MeckPetarda/bachelor/write/outline/3.3_firmware.md

# OSNOVA PLUS - 3.3 firmware

---

- Firmware is written in C using ESP-IDF v5.x with FreeRTOS; the entire application runs on a single ESP32-WROOM-32
  module
- The dual-core Xtensa LX6 architecture allows separation of concerns: the WiFi stack is pinned to Core 0 by ESP-IDF
  configuration, leaving Core 1 available for application logic including RFID communication and the main task loop (per
  ESP32 TRM Section 1.1)
- The firmware is identical across all Lighthouse units - no unit-specific configuration is compiled in; all per-device
  settings (WiFi credentials, MQTT broker address, lighthouse identity) are configured at runtime via the provisioning
  system and stored in NVS

## 3.3.1 system initialization and WiFi provisioning

- On boot, the firmware executes a sequential initialization: GPIO configuration -> battery monitor -> WiFi provisioning
  (credentials load + STA connection) -> SNTP time synchronisation (broker IP as NTP server) -> MQTT client -> offline
  event logger -> RFID reader -> main task loop
- If the device has never been configured (no credentials in NVS), the boot sequence blocks after GPIO initialization
  and waits for the user to trigger provisioning via a 5-second hold of BUTTON2

### Provisioning flow

- Provisioning is triggered by a 5-second hold of BUTTON2, which sets a flag in RTC memory and calls `esp_restart()`; on
  the subsequent boot, the firmware detects the flag and enters AP mode instead of STA mode
- In AP mode, the device broadcasts an open WiFi network ("Lighthouse-Setup") and starts an HTTP server on port 80
  serving a minimal HTML configuration form from firmware flash via the SPIFFS virtual filesystem
- A lightweight DNS server responds to all DNS queries with the device's AP IP address (192.168.4.1), enabling captive
  portal detection on iOS, Android, Windows, and macOS; the user's device automatically opens a browser to the
  provisioning page
- The form collects four fields: WiFi SSID, WiFi password, MQTT broker IP, and MQTT broker port; client-side JavaScript
  validates input format before submission
- On form submission, the device attempts a STA connection with the provided WiFi credentials; if successful, it tests
  MQTT connectivity; results are reported back to the browser via a JSON response
- The browser displays success/failure and a restart button; the device only restarts when the user explicitly clicks
  restart, ensuring the browser receives the response before the AP shuts down
- Credentials are encrypted with AES-128-ECB via the mbedTLS library, which utilises the ESP32 hardware AES accelerator
  (per ESP32 TRM Section 14), and stored in a dedicated NVS partition; on subsequent boots, credentials are loaded from
  NVS and used for automatic STA connection

Figure 3.3.1-1: Provisioning state machine diagram - states: UNCONFIGURED, SETUP_REQUESTED, AP_ACTIVE, CONNECTING, CONNECTED, OFFLINE; transitions labelled with triggering events (button press, credential submission, connection success/failure, reboot)

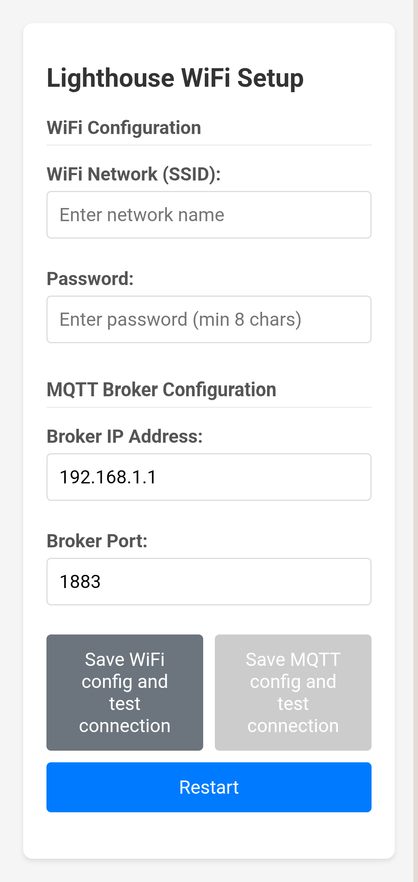
[picture p8: write/outline/images/3.3.1-2_page.png]
Figure 3.3.1-2: Screenshot of the provisioning web form as rendered on a mobile device - showing WiFi SSID/password fields, MQTT broker IP/port fields, test buttons, and status display area


## 3.3.2 UHF RFID scan control

- The YPD-R300 UHF RFID reader module communicates with the ESP32 via UART at 115 200 baud (per R300 Protocol Section
  1.2)
- RFID scanning uses the real-time inventory command `cmd 0x89` (`cmd_name_real_time_inventory`) with channel parameter
  `0xFF` (minimized inventory duration) and 10 ms inter-round delay (per R300 Protocol Section 2.2.8)
- In real-time inventory mode, the reader streams tag detection packets as they occur rather than buffering them
  internally; each packet contains the tag's EPC, RSSI, frequency/antenna ID, and protocol control (PC) word
- A scan window lasts approximately 5 seconds, producing ~60 individual tag detections per window under typical
  conditions

### IR-triggered scanning

- The AM312 PIR sensor on GPIO19 detects motion in the doorway and triggers RFID scan bursts via a GPIO interrupt
  (rising edge, `IRAM_ATTR` ISR handler)
- On IR trigger, the firmware powers on the R300 module via the BC337-25 transistor switch, performs a UART handshake to
  verify reader responsiveness, and starts real-time inventory
- The scan burst runs for `IR_SCAN_DURATION_MS` (default 5 s); if additional IR triggers arrive during an active
  burst, the timer is restarted without interrupting the ongoing inventory - this extends the scan window when a person
  lingers in the doorway
- When the burst timer expires with no further IR triggers, the inventory is stopped and the R300 module is powered off
  to conserve energy

### MQTT batch accumulator

- To avoid saturating the MQTT connection with ~60 individual publishes during a 5-second scan window, detections are
  accumulated in a time-windowed batch buffer on the firmware side
- The accumulator collects tag detections for up to `scan_batch_ms` (default 150 ms, configurable 50-2 000 ms) or until
  the buffer reaches `MQTT_SCAN_BATCH_MAX_ENTRIES`, then flushes the batch as a single JSON array to MQTT topic
  `lighthouse/{id}/scans`
- Each element in the flushed array carries its individual `epc`, `rssiDbm`, `antennaId`, `frequency`, and `deviceId`
  fields; the `timestampMs` and `timeBasis` fields are computed once at flush time and are shared across all elements in
  the batch - timestamp resolution is therefore bounded by the batch interval (minimum 50 ms, default 150 ms)
- The live scan publish path uses QoS 1 to reduce the four-way handshake overhead of QoS 2; the offline replay path
  retains QoS 2 for exactly-once delivery of historically cached events

### Power cap discovery

- The YPD-R300 hardware power cap is 25 dBm, despite the datasheet specifying 33 dBm; the `set_power(33)` command
  returns error code `0x48` (parameter out of range) which was initially ignored due to missing response validation
- The firmware now reads and validates all R300 command responses; transmit power is clamped to the 20-25 dBm range

## 3.3.3 timekeeping and timestamp quality

- The ESP32 does not include a battery-backed hardware RTC; after a power cycle, the system clock starts from an
  undefined epoch and must be synchronised via SNTP before timestamps are meaningful
- The firmware implements a three-tier time quality model to ensure that every event payload declares the
  trustworthiness of its timestamp

**Table 3.3.3-1** - Time quality tiers

| Quality level | `timeBasis` value | Condition | Accuracy |
| --- | --- | --- | --- |
| Synced | `synced` | SNTP synchronisation completed successfully | Millisecond-level (network + NTP jitter) |
| Estimated | `estimated` | No SNTP sync yet, but last-known-good time recovered from NVS | Seconds to minutes (RTC drift ~5 % at 150 kHz; per ESP32 Datasheet Section 3.3.4) |
| Relative | `relative` | No NVS time available; first boot or NVS lost | Boot-relative milliseconds only; not a real wall-clock time |

### SNTP synchronisation

- The firmware uses the ESP-IDF SNTP client in polling mode against a chrony NTP server on the local network
- On successful sync, a callback upgrades the time quality to `synced` and persists the current Unix timestamp alongside
  the ESP32 uptime counter to NVS; this pair allows the next boot to estimate wall-clock time even before SNTP completes
- Timezone is set to CET/CEST (`TZ=CET-1CEST,M3.5.0,M10.5.0/3`) before SNTP initialisation so that `localtime()` returns
  correct local time immediately on sync

### Offline degradation

- If SNTP sync does not complete (e.g. NTP server unreachable), the firmware continues operating with `estimated` or
  `relative` timestamps
- The `timeBasis` field is attached to every scan event payload; the server uses this to decide whether scans are
  eligible for direction detection processing - non-synced scans are handled by the orphan processing logic on the
  server side

## 3.3.4 MQTT communication and offline caching

### MQTT client

- The firmware connects to the MQTT broker using the `esp_mqtt_client` component with connection parameters loaded from
  NVS (broker IP and port configured during provisioning)
- The MQTT client ID is derived from the ESP32's eFuse MAC address, ensuring uniqueness across devices (per ESP32 TRM
  Section 4.4)
- A Last Will and Testament (LWT) message is registered on connect, allowing the server to detect unexpected
  disconnections

**Table 3.3.4-1** - MQTT topics and QoS levels

| Topic | Direction | QoS | Content |
| --- | --- | --- | --- |
| `lighthouse/{id}/scans`  | Publish (live) | 1 | Batched JSON array of tag detections |
| `lighthouse/{id}/scans`  | Publish (replay) | 2 | Replayed offline-cached events |
| `lighthouse/{id}/health` | Publish | 1 | Periodic health telemetry (system, RFID, battery) |
| `lighthouse/{id}/config` | Subscribe | 1 | Runtime configuration updates from server |

### Offline event caching

- When the MQTT connection is unavailable, tag detections are stored to a dedicated LittleFS partition on the ESP32's
  flash memory; this is a separate partition from the SPIFFS partition used by the provisioning HTML - SPIFFS is a
  read-only image compiled into the firmware binary, while LittleFS is a writable filesystem used exclusively for
  offline event storage
- Events are written to a ring buffer file (`events.bin`) with CRC32 validation per entry; write and read indices are
  persisted to both RTC memory (survives soft reset) and NVS (survives power loss)
- On MQTT reconnection, a background replay task reads cached events and publishes them at a throttled rate (max 10
  events/second) with QoS 2, adding an `offline: true` flag and a `replayTime` field to each payload
- The replay task runs at lower priority than the main logging task, ensuring real-time detections are not delayed by
  replay activity

Figure 3.3.4-1: Offline caching and replay sequence diagram - tag detected while offline -> event queued -> logging task writes to LittleFS ring buffer -> NVS pointers updated -> MQTT reconnects -> replay task reads from ring buffer -> publishes with offline flag -> server ingests as normal scan wi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

## 3.3.5 user interaction: buttons, LEDs, and gestures

- The IO subsystem manages four LEDs, two buttons, and one IR sensor; all IO logic is encapsulated in a dedicated
  `io_controller` module, keeping the main application file (`lighthouse.c`) limited to orchestration and MQTT/offline
  routing

**Table 3.3.5-1** - GPIO pin assignments

| Constant | GPIO | Function |
| --- | ---- | --- |
| LED1_PIN | 4 | WiFi + MQTT combined status (green) |
| LED2_PIN | 21 | IR mode / AP provisioning indicator (green) |
| SCANNING_LED  | 26 | Active RFID scan indicator (red) |
| ACTIVITY_LED  | 25 | Tag detection flash / battery status (yellow) |
| BUTTON1_PIN | 22 | Scan mode control |
| BUTTON2_PIN | 23 | Status message / WiFi setup trigger |
| IR_SENSOR_PIN | 19 | AM312 PIR motion sensor |

- GPIO22 and GPIO23 (buttons) use external pull-up resistors; debounce filtering is applied in software with a 50 ms
  debounce threshold

### Scan modes

- The firmware operates in one of two scan modes, selectable via BUTTON1 3-second hold:

**Table 3.3.5-2** - Scan mode behavior

| Mode | LED2 state | IR sensor | BUTTON1 short press | Entry condition |
| --- | --- | --- | --- | --- |
| IR Mode (default) | Solid on | Active - triggers 5 s scan bursts | No-op | 3 s hold from Manual / Boot |
| Manual Mode | Off | Ignored | Toggle RFID on/off  | 3 s hold from IR Mode |

- RFID scanning is always stopped and the reader powered off before any mode transition

Figure 3.3.5-1: Scan mode state machine - two states (IR Mode, Manual Mode); transitions: 3-second BUTTON1 hold in either direction; entry actions listed for each state (stop RFID, set LED2, enable/disable IR)

### Button gestures

**Table 3.3.5-3** - Complete button gesture reference

| Button  | Gesture | Action |
| --- | --- | --- |
| BUTTON1 | Short press | Toggle RFID scan (Manual Mode only; no-op in IR Mode) |
| BUTTON1 | 3 s hold | Switch between IR Mode and Manual Mode |
| BUTTON2 | Short press | Publish status/statistics message via MQTT |
| BUTTON2 | 5 s hold | Enter WiFi AP provisioning (triggers reboot into setup mode) |
| Both | 10 s hold | Cache purge: clear offline event cache, confirmation LED sequence, restart |

### Cache purge combo gesture

- Holding both buttons simultaneously for 10 seconds triggers a developer cache purge gesture
- During the hold, LEDs illuminate sequentially as a countdown: LED1 at 2.5 s, LED2 at 5 s, ACTIVITY_LED at 7.5 s
- At 10 s, `offline_logger_clear_all()` resets the ring buffer pointers; a confirmation flash sequence (each LED flashed
  in order, 200 ms on/off) plays before `esp_restart()`
- Releasing either button before the 10-second threshold cancels the gesture and restores normal LED states
- While the combo gesture is active, RFID scanning is stopped and IR triggers are suppressed

### LED indicator behavior

**Table 3.3.5-4** - LED states during normal operation

| LED | Condition | State |
| --- | --- | --- |
| LED1 (green) | No WiFi connection | Off |
| LED1 (green) | WiFi connected, no MQTT | Blinking 1 s period |
| LED1 (green) | WiFi + MQTT connected | Solid on |
| LED2 (green) | IR Mode active | Solid on |
| LED2 (green) | Manual Mode active | Off |
| SCANNING_LED (red) | RFID inventory in progress | On |
| SCANNING_LED (red) | No active inventory | Off |
| ACTIVITY_LED (yellow) | Tag detected | Brief 100 ms flash  |

**Table 3.3.5-5** - LED states during AP provisioning

| LED | Provisioning phase | State |
| --- | --- | --- |
| LED1 (green) | AP active, WiFi test not yet passed | Blinking |
| LED1 (green) | WiFi test passed | Solid on |
| LED2 (green) | AP active, MQTT test not yet passed | Blinking |
| LED2 (green) | MQTT test passed | Solid on |

### Battery status LED patterns (ACTIVITY_LED, battery power only)

| Battery level  | LED pattern |
| --- | --- |
| USB powered | Off (tag detection flashes only) |
| Battery > 10 % | Brief flash every 5 seconds |
| Battery 5-10 % | Pulsing 500 ms on/off |
| Battery < 5 %  | Rapid pulsing 200 ms on/off |

- The battery LED patterns run in a dedicated FreeRTOS task and do not interfere with the brief 100 ms tag detection
  flashes on the same LED
