MeckPetarda/bachelor/presentation/beta/Beta.odp

## EMBEDDED ŘEŠENÍ DOCHÁZKOVÉHO SYSTÉMU PRO INTEGRACI DO PODNIKOVÉ APLIKACE

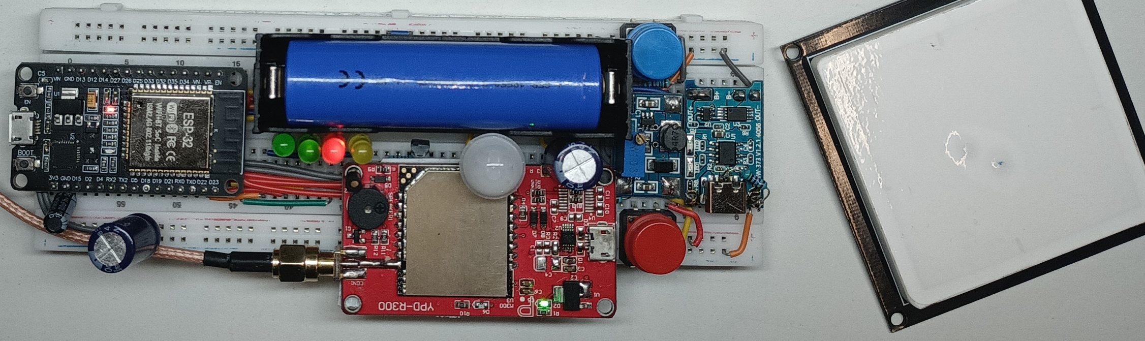
[picture p11: figure]

Ústav mechaniky těles, mechatroniky a biomechaniky
Fakulta strojního inženýrství, Vysoké učení technické v Brně

2026

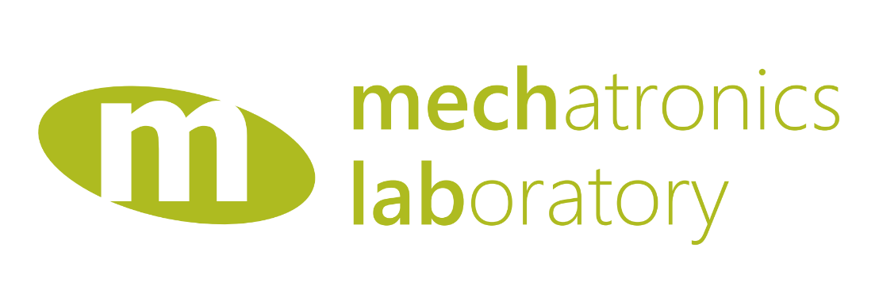
[picture p12: figure]

Autor práce: Jakub Hloušek

Vedoucí práce: Ing. Michal Bastl, Ph.D

Autor práce: Jakub Hloušek

Vedoucí práce: Ing. Michal Bastl, Ph.D

Notes: <number>

## Zadání a cíle

1. Rešerše aktuálních řešení a technologií
2. Návrh architektury docházkového systému
3. Implementace prototypu zahrnujícího identifikační modul (RFID/NFC/PIN)
4. Ověření funkčnosti řešení v modelové kancelářské situaci

0<number> / 11

## Motivace – stávající systémy

Čipové (RFID, PIN)

- jedno čidlo
- krátká vzdálenost pro sken

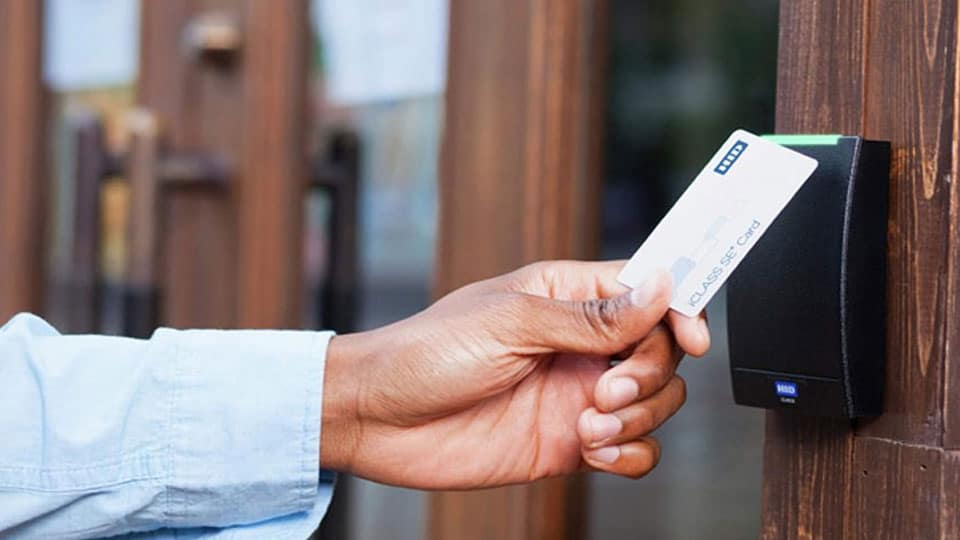
[picture p13: figure]

Biometrické

- vysoká cena
- práce s citlivými informacemi

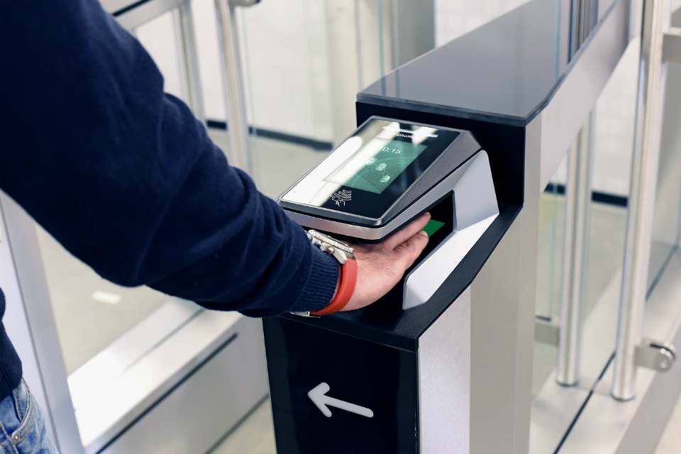
[picture p14: figure]

0<number> / 11

## Motivace – navrhnuté řeření

- Dvě čipové brány s technologií UHF RFID
- Pasivní sken čipu na 2-3m (dle antény)
- Levné provedení
- Nepracuje s citlivými informacemi

0<number> / 11

## Motivace – navrhnuté řeření


- Dvě čipové brány s technologií UHF RFID
- Pasivní sken čipu na 2-3m (dle antény)
- Levné provedení
- Nepracuje s citlivými informacemi

0<number> / 11

## Co je hotovo

- 2x Prototyp UHF RFID majáků na breadboardech
- Navržena DPS - připravena k osazení
- Funkční firmware pro ESP-32
- Přenos informací na server
- Koncept webového klienta s debugem skenů

0<number> / 11

## Slide 7

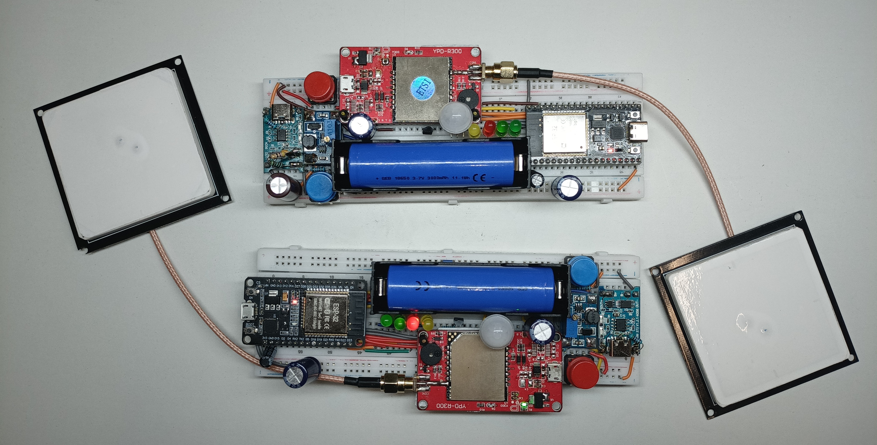
[picture p15: figure]

0<number> / 11

## Slide 8

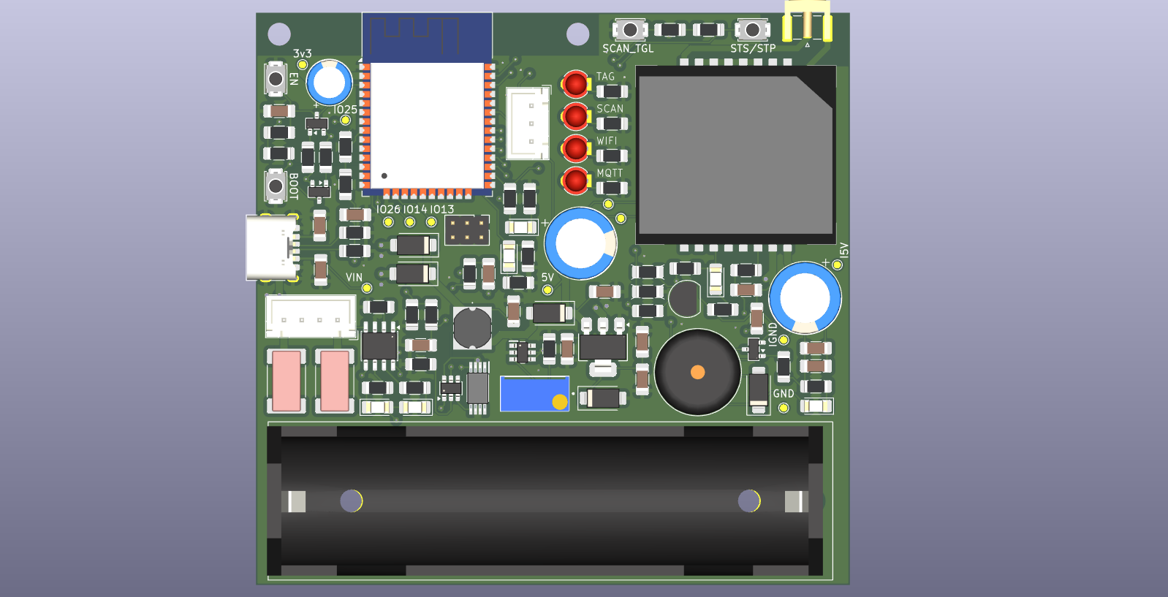
[picture p16: figure]

0<number> / 11

## Co je v plánu

- Osazení desky
- Vytvoření pouzdra pro maják
- Správa uživatelů a majáků na webu
- Zpracování surových dat na časové bloky
- Integrace s externím softwarem

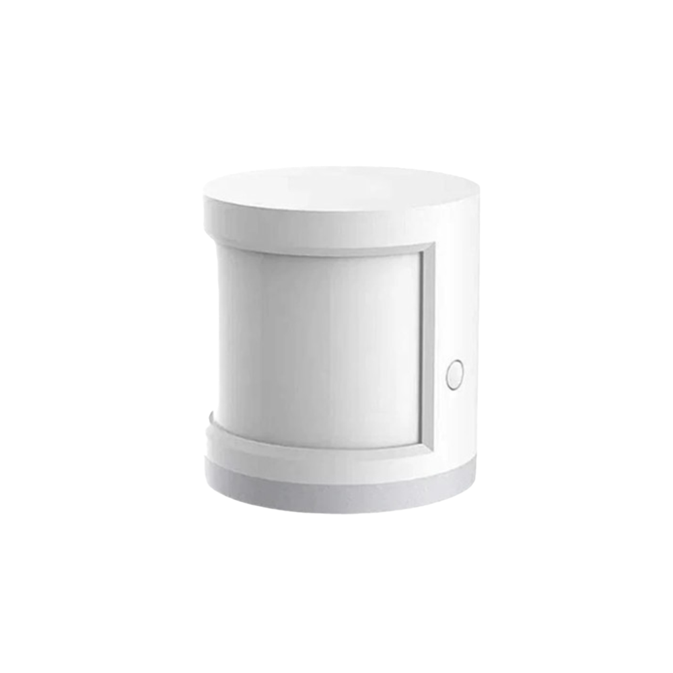
[picture p17: figure]

0<number> / 11

## Současný stav

Hardware

Software

Praktický test

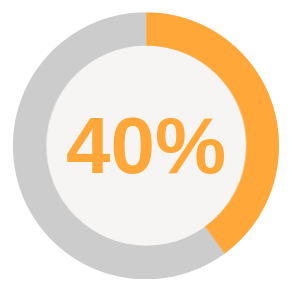
[picture p18: figure]
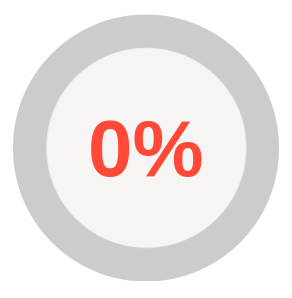
[picture p19: figure]

Firmware

Návrh pouzdra

Napsat práci

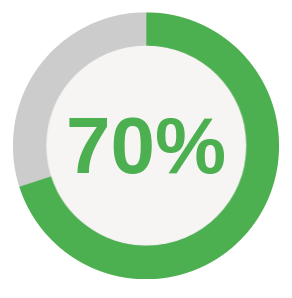
[picture p20: figure]
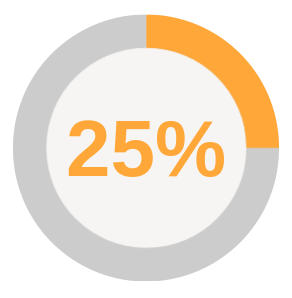
[picture p21: figure]

<number> / 11

## Děkuji za pozornost

Ústav mechaniky těles, mechatroniky a biomechaniky
Fakulta strojního inženýrství, Vysoké učení technické v Brně

2026

Autor práce: Jakub Hloušek

Vedoucí práce: Ing. Michal Bastl, Ph.D

Notes: <number>
