MeckPetarda/bachelor/docs/pinout.webp

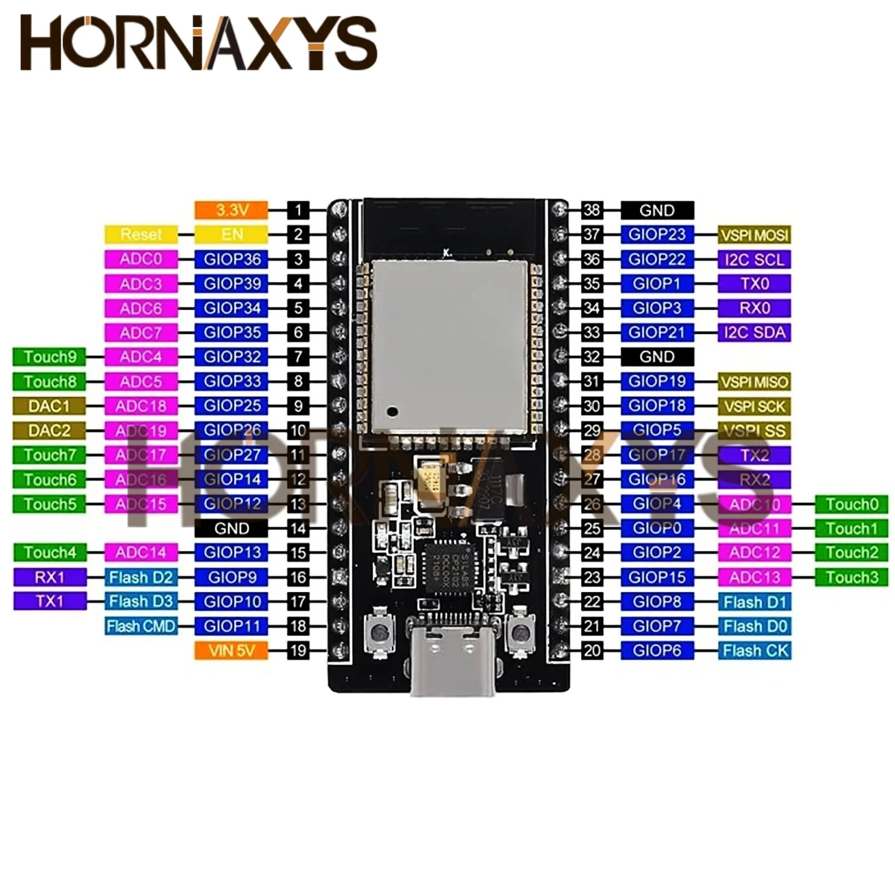
docs/pinout.webp
