MeckPetarda/bachelor/write/thesis/images/board_v2_schematic.png

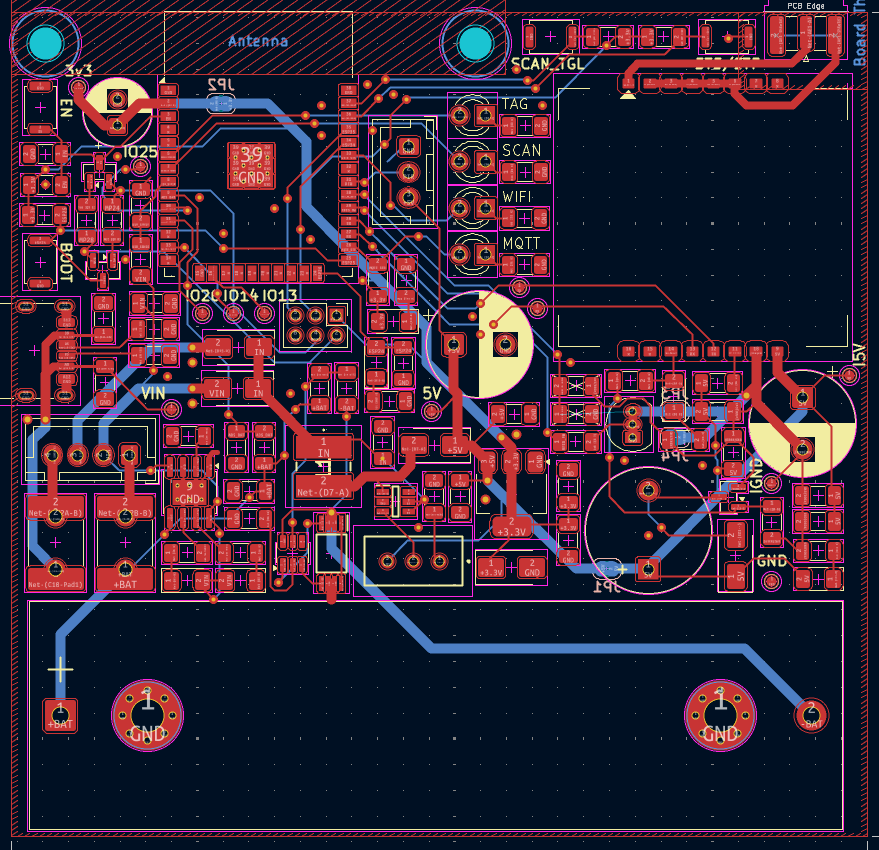
write/thesis/images/board_v2_schematic.png
