MeckPetarda/bachelor/write/thesis/images/kicad_render.png

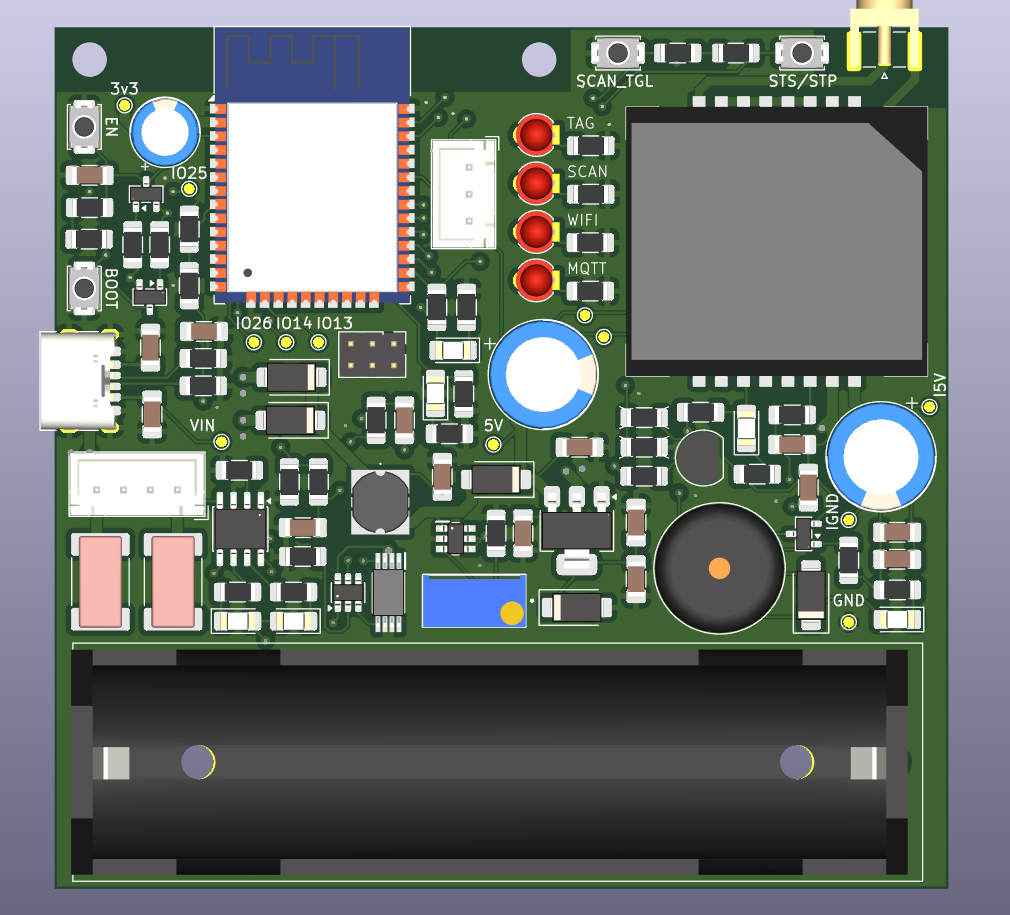
write/thesis/images/kicad_render.png
