MeckPetarda/bachelor/write/thesis/images/lighthouses.jpg

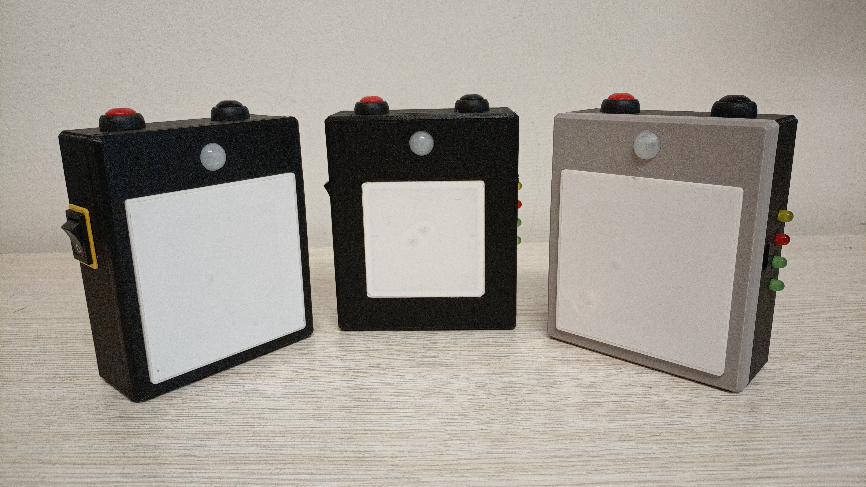
write/thesis/images/lighthouses.jpg
