MeckPetarda/bachelor/write/thesis/images/kicad_render_vs_assembly.png

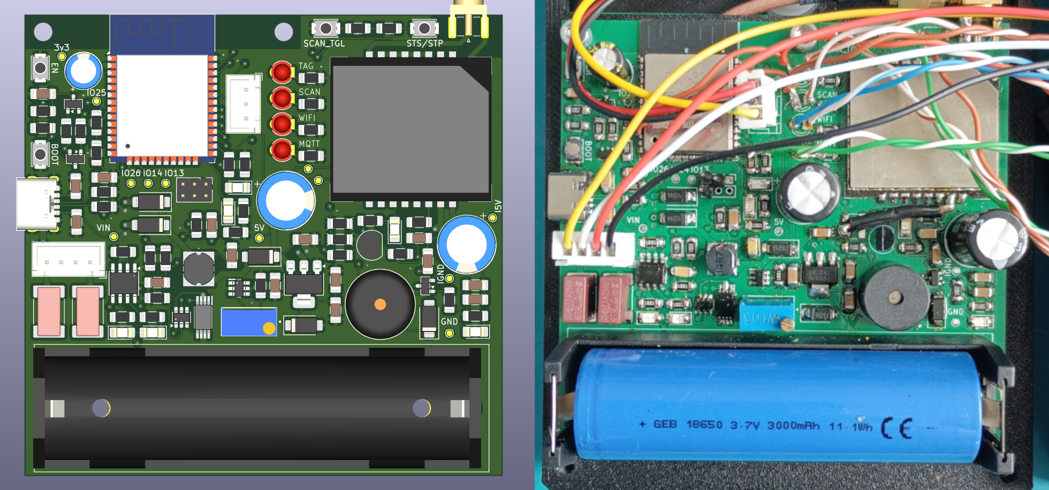
write/thesis/images/kicad_render_vs_assembly.png
