MeckPetarda/bachelor/circuits/lighthouse/lighthouse_v2.pdf

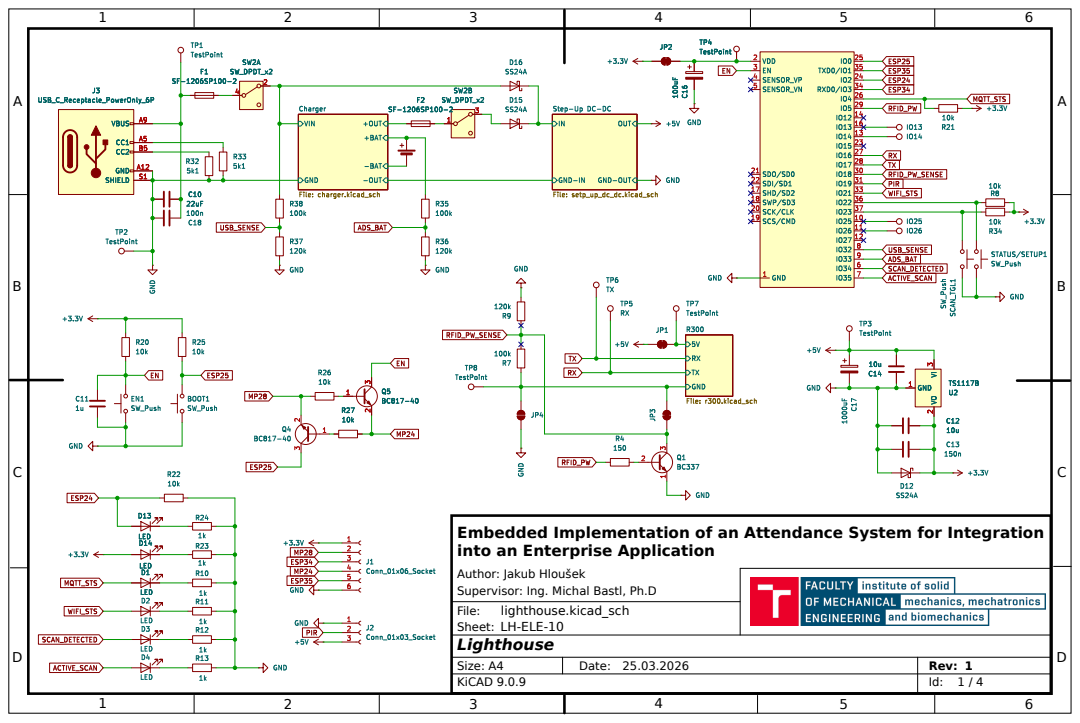
[picture p52: page 1]
Size: A4; Date: 25.03.2026; Rev: 1; LH-ELE-10; lighthouse.kicad_sch

Embedded Implementation of an Attendance System for Integration
into an Enterprise Application
Author: Jakub Hloušek
Supervisor: Ing. Michal Bastl, Ph.D
File:
Sheet:
Lighthouse
KiCAD 9.0.9

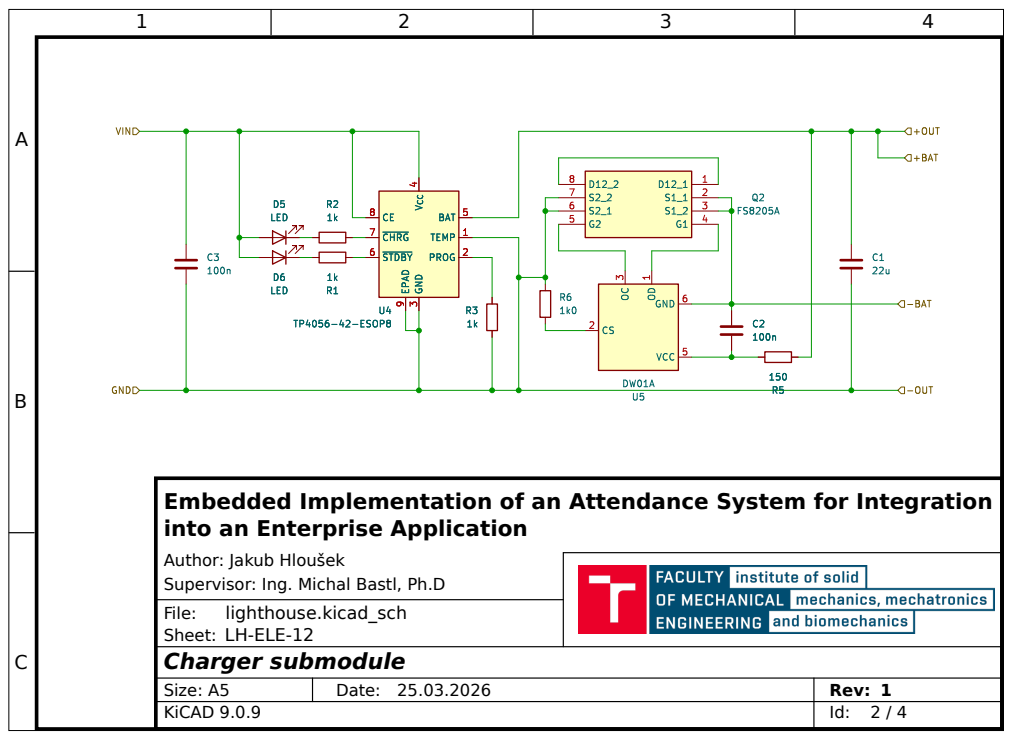
[picture p53: page 2]
Size: A5; Date: 25.03.2026; Rev: 1; LH-ELE-12; lighthouse.kicad_sch

Embedded Implementation of an Attendance System for Integration
into an Enterprise Application
Author: Jakub Hloušek
Supervisor: Ing. Michal Bastl, Ph.D
File:
Sheet:
Charger submodule

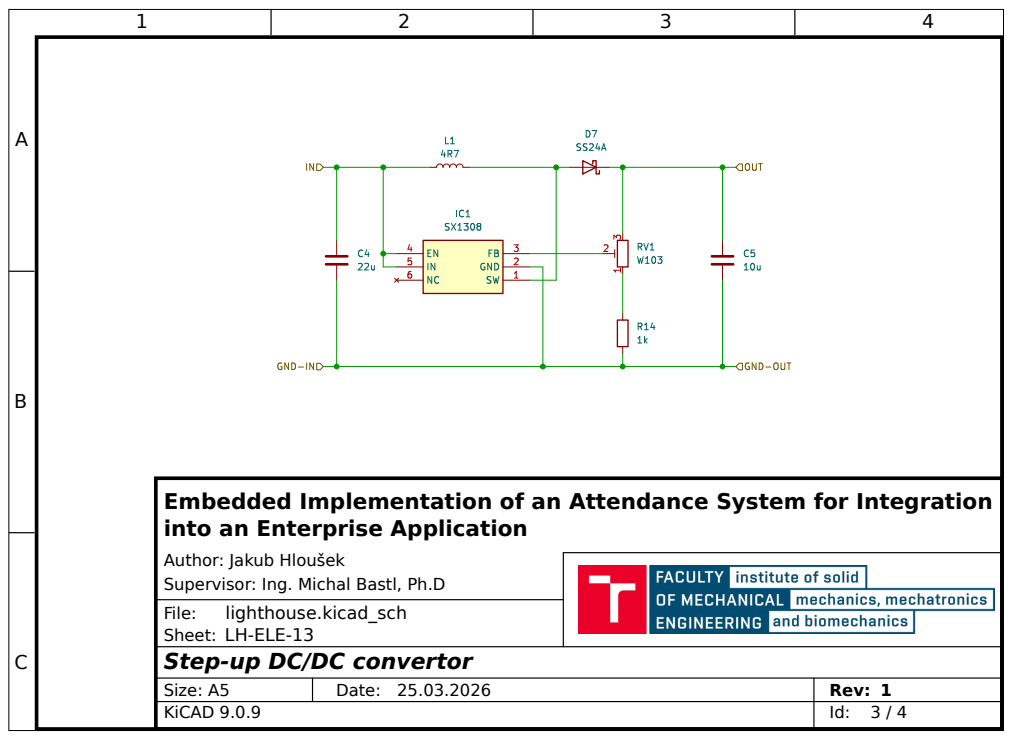
[picture p54: page 3]
ion; Size: A5; Date: 25.03.2026; Rev: 1; LH-ELE-13; lighthouse.kicad_sch

Embedded Implementation of an Attendance System for Integration
into an Enterprise Application
Author: Jakub Hloušek
Supervisor: Ing. Michal Bastl, Ph.D
File:
Sheet:
Step-up DC/DC convertor

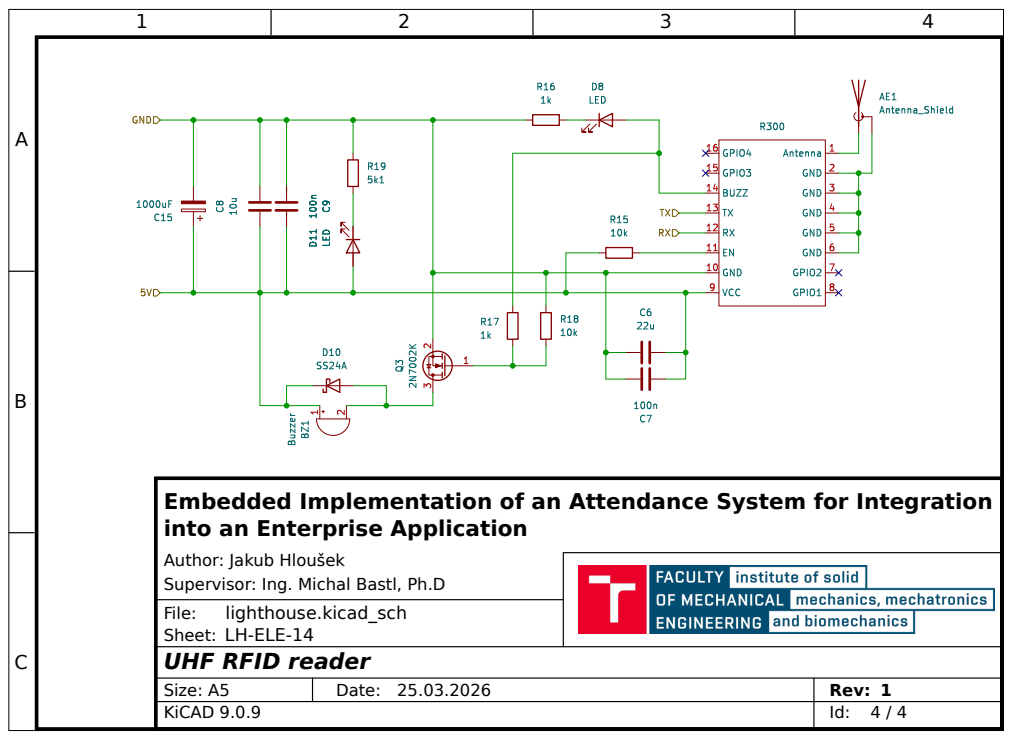
[picture p55: page 4]
Size: A5; Date: 25.03.2026; Rev: 1; LH-ELE-14; lighthouse.kicad_sch

Embedded Implementation of an Attendance System for Integration
into an Enterprise Application
Author: Jakub Hloušek
Supervisor: Ing. Michal Bastl, Ph.D
File:
Sheet:
UHF RFID reader
