MeckPetarda/bachelor/write/thesis/images/antenna_joint_comparison.png

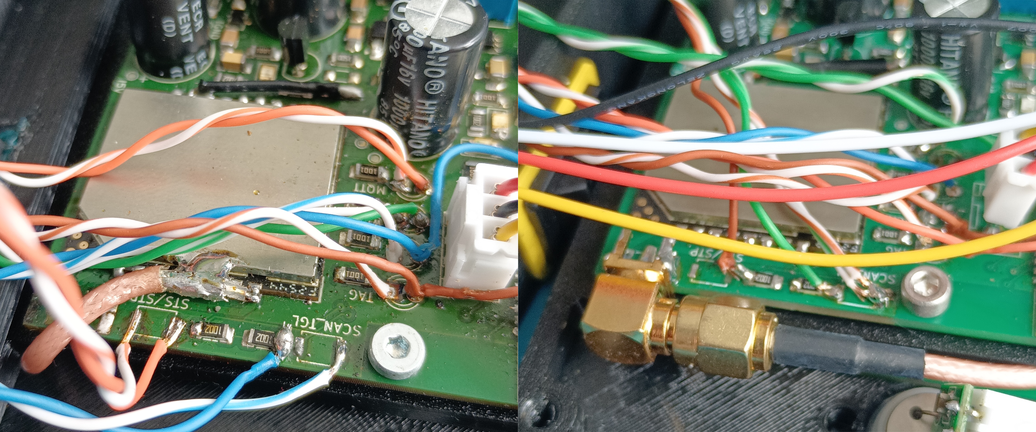
write/thesis/images/antenna_joint_comparison.png
